GenericLab/o--Indosluch.EM--o/LM386_Indosluch_DIY/Early Versions/handDrawn_Indosluch.png

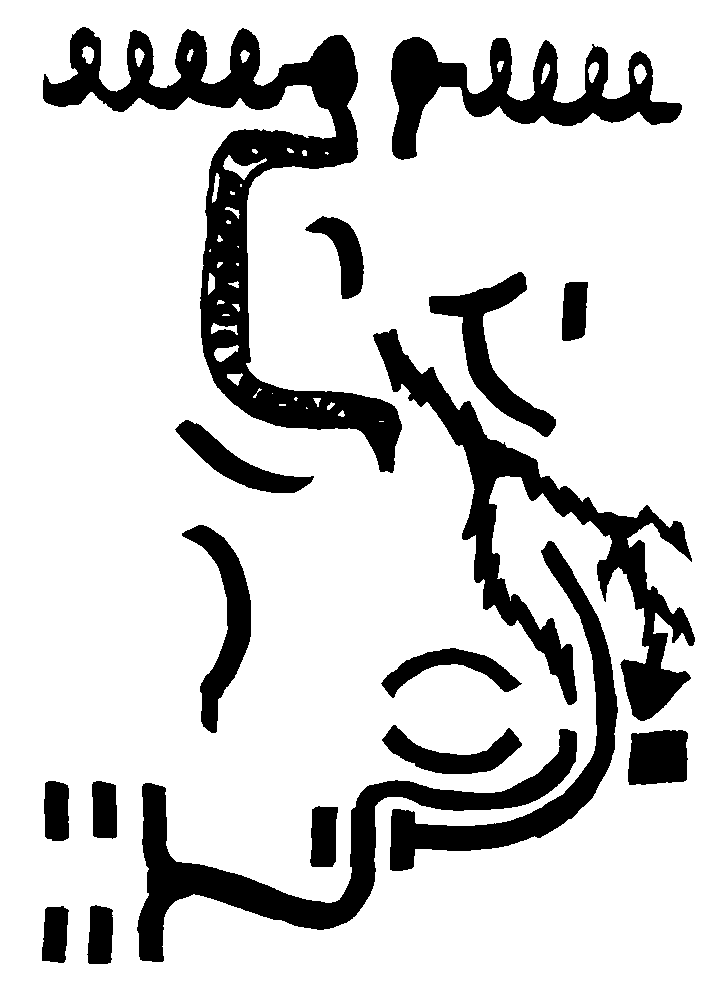
LM386_Indosluch_DIY/Early Versions/handDrawn_Indosluch.png
