GenericLab/o--Indosluch.EM--o/LM386_Indosluch_DIY/Early Versions/MASK_LM386_Indosluch_DIY.png

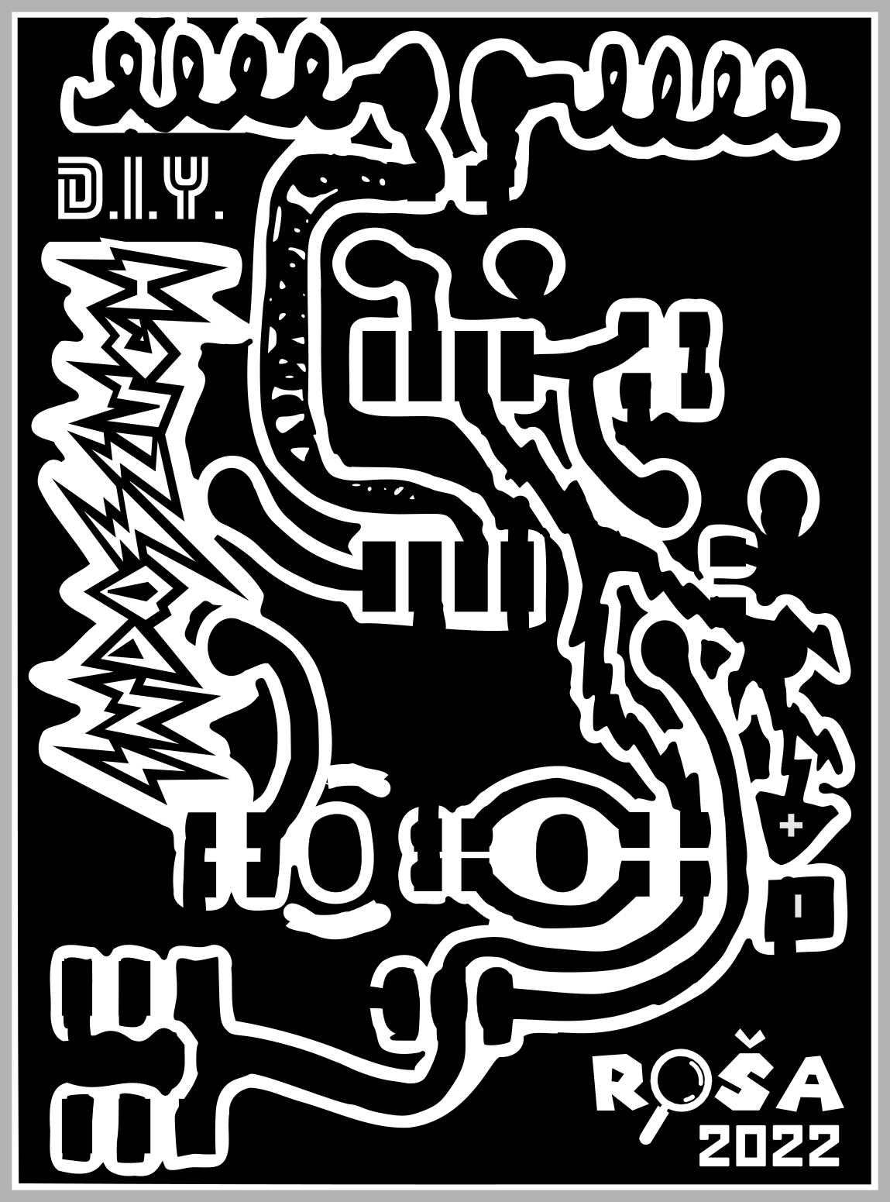
LM386_Indosluch_DIY/Early Versions/MASK_LM386_Indosluch_DIY.png
