GenericLab/o--Indosluch.EM--o/LM386_Indosluch_DIY/Engraving_Indosluch_DIY.png

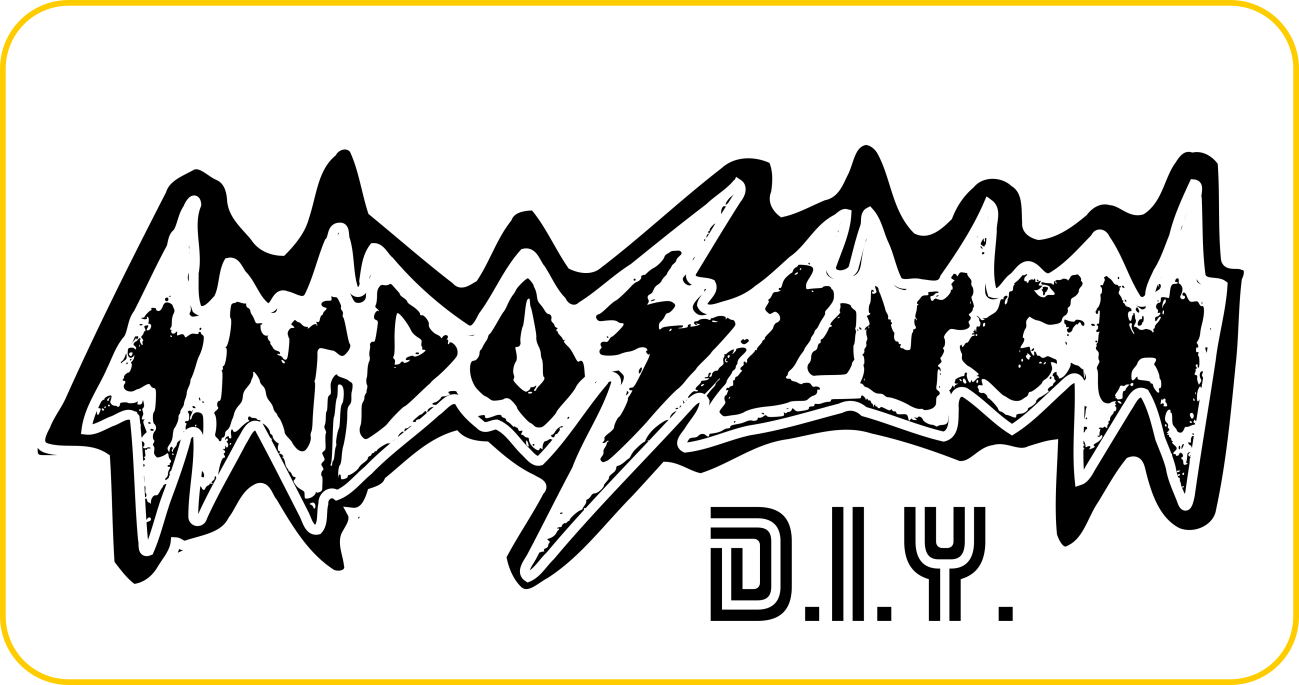
LM386_Indosluch_DIY/Engraving_Indosluch_DIY.png
