GenericLab/o--Indosluch.EM--o/sources/ErrorLeaks/reverseEng_error-zapper.jpg

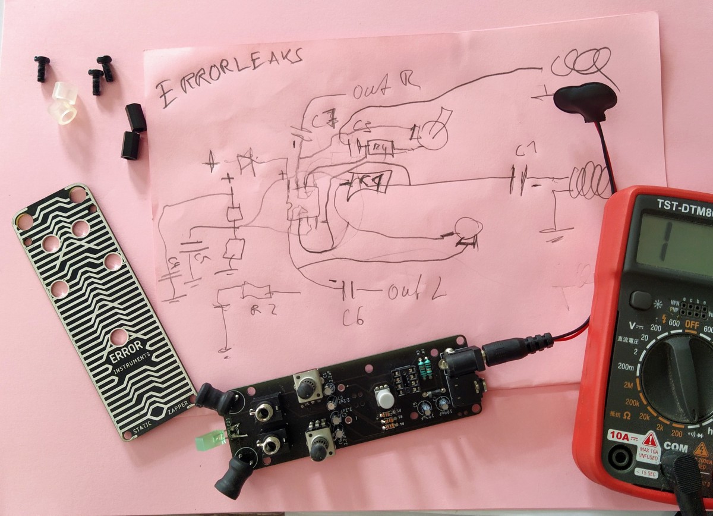
sources/ErrorLeaks/reverseEng_error-zapper.jpg
