GenericLab/o--Indosluch.EM--o/sources/ErrorLeaks/schema_error-zapper.jpg

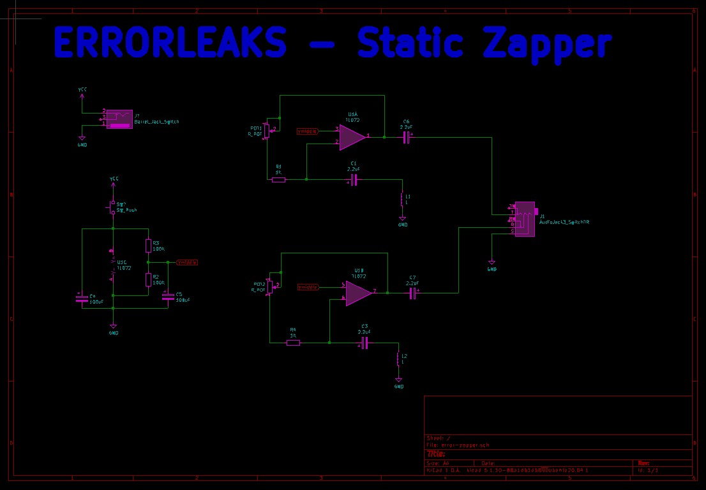
sources/ErrorLeaks/schema_error-zapper.jpg
