GenericLab/o--Indosluch.EM--o/sources/Franzis_Bat-Detector/Fledermaus11.jpg

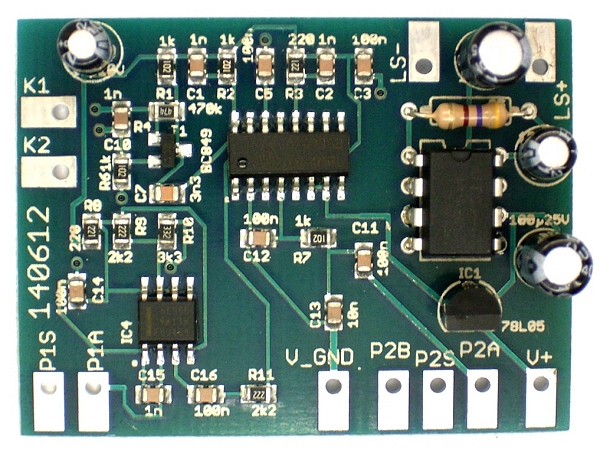
sources/Franzis_Bat-Detector/Fledermaus11.jpg
