GenericLab/o--Indosluch.EM--o/sources/MartinHowse_Detektor/1010_Detektor.jpg

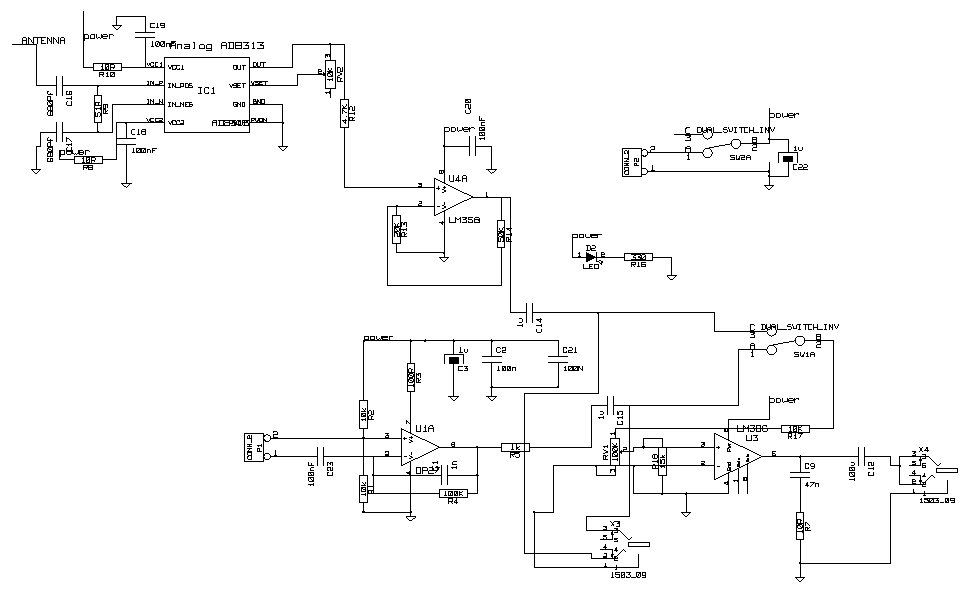
sources/MartinHowse_Detektor/1010_Detektor.jpg
