GenericLab/o--Indosluch.EM--o/sources/SOMA-EtherLeaks/Ether_ampStage.jpg

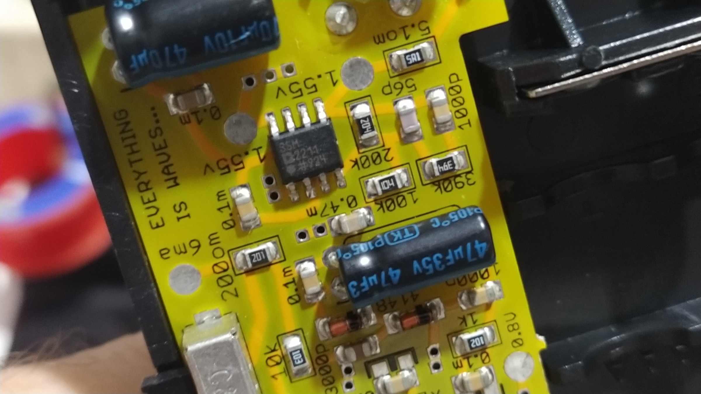
sources/SOMA-EtherLeaks/Ether_ampStage.jpg
