GenericLab/o--Indosluch.EM--o/sources/SOMA-EtherLeaks/Ether_AntennaArea.jpg

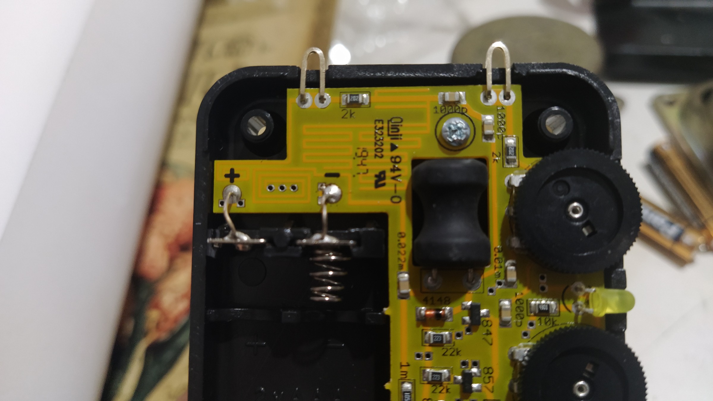
sources/SOMA-EtherLeaks/Ether_AntennaArea.jpg
