GenericLab/o--Indosluch.EM--o/sources/SOMA-EtherLeaks/Ether_Backside_full.jpg

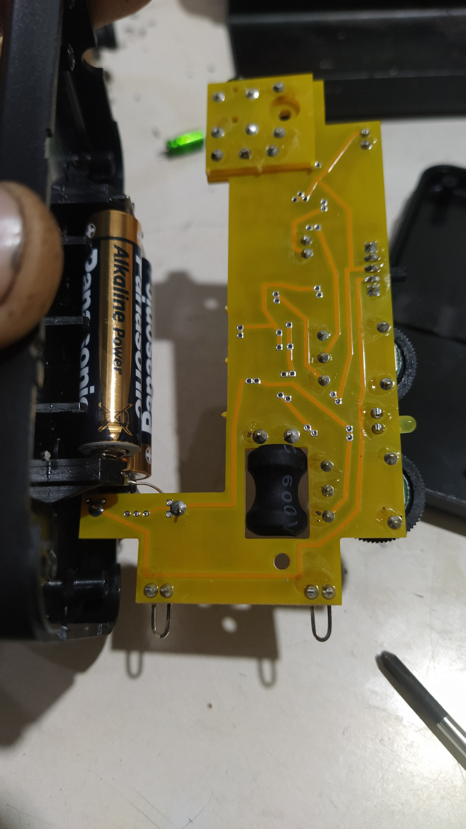
sources/SOMA-EtherLeaks/Ether_Backside_full.jpg
