GenericLab/o--Indosluch.EM--o/sources/SOMA-EtherLeaks/Ether_FrontSideFull.jpg

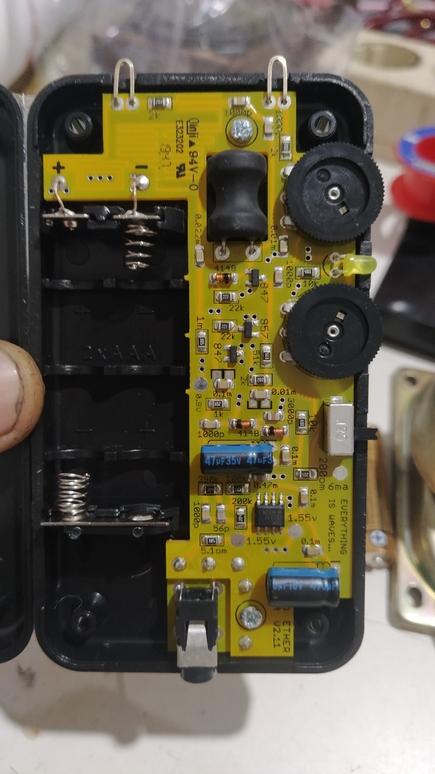
sources/SOMA-EtherLeaks/Ether_FrontSideFull.jpg
