GenericLab/o--Indosluch.EM--o/sources/Uwes_circuits/LM386 sniffer_ac.jpg

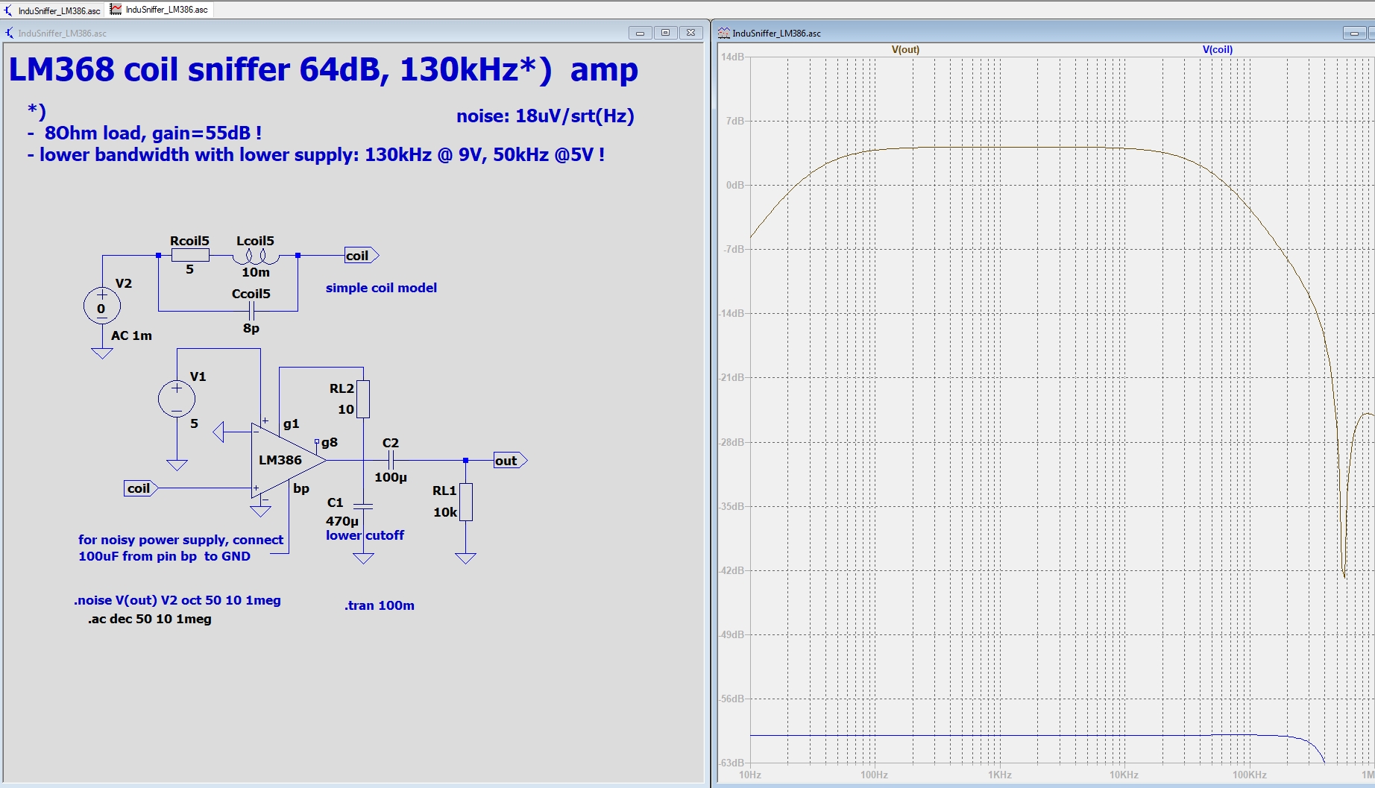
sources/Uwes_circuits/LM386 sniffer_ac.jpg
