GenericLab/o--Indosluch.EM--o/sources/Uwes_circuits/LM386 sniffer_noise.jpg

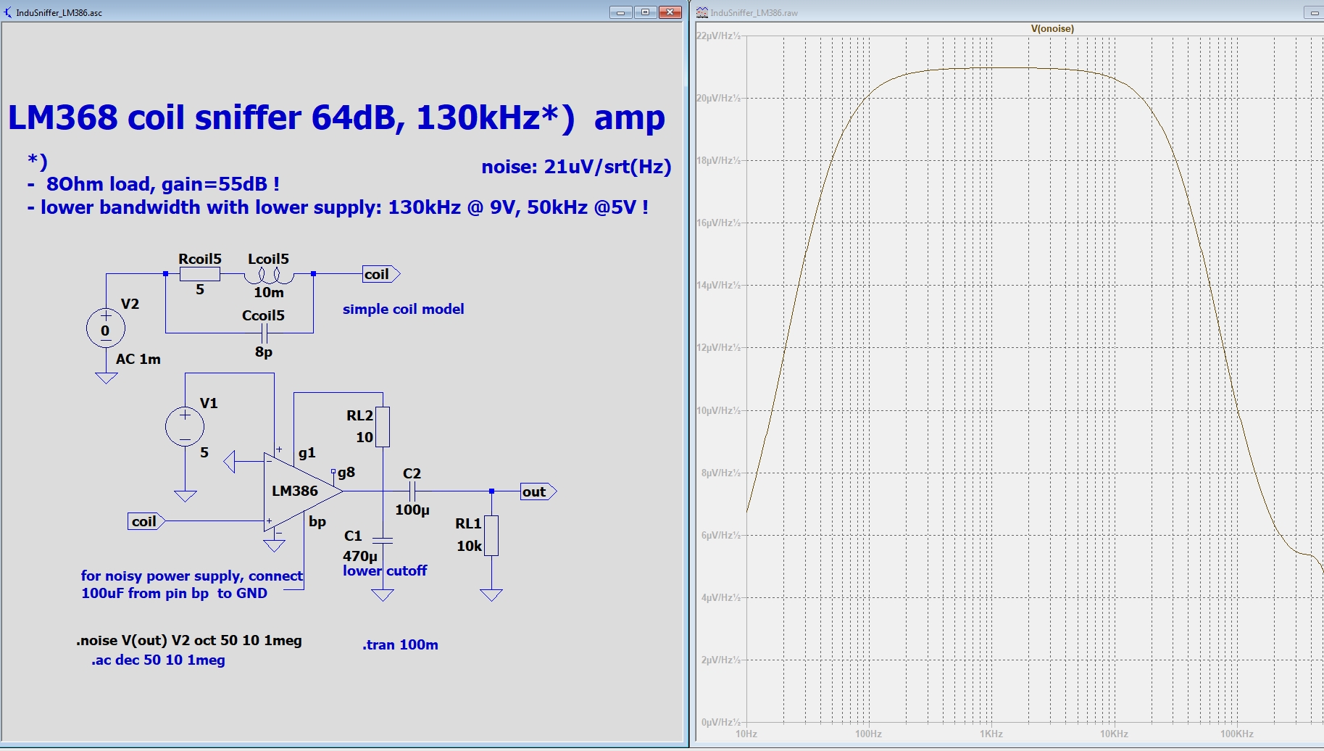
sources/Uwes_circuits/LM386 sniffer_noise.jpg
