GenericLab/o--Indosluch.EM--o/sources/Uwes_circuits/lm386.gif

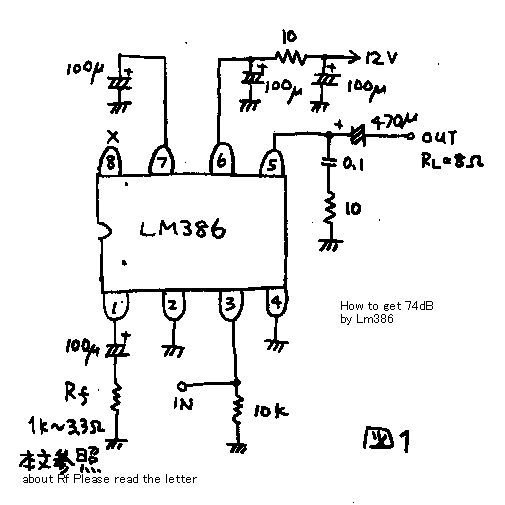
sources/Uwes_circuits/lm386.gif
