GenericLab/o--Indosluch.EM--o/sources/Uwes_circuits/NPN-PNP- sniffer_ac.jpg

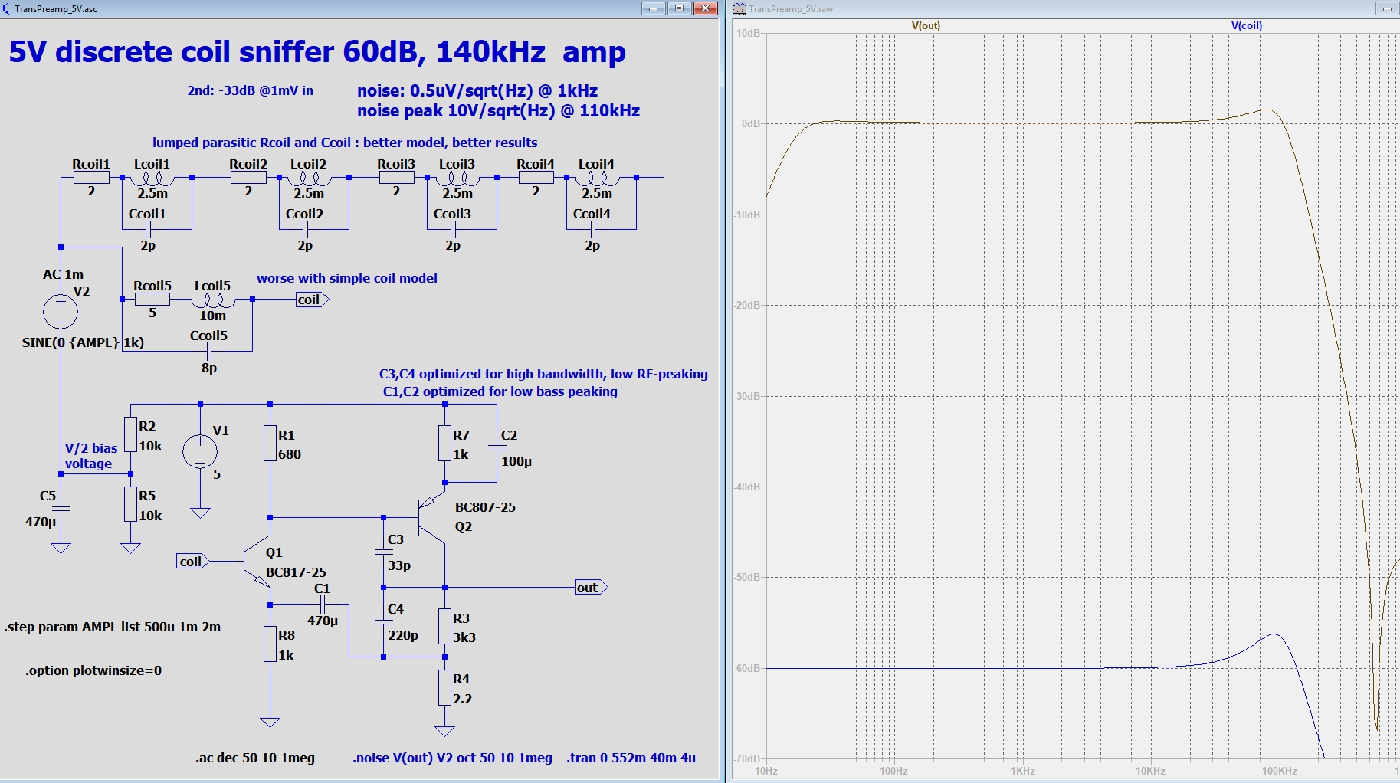
sources/Uwes_circuits/NPN-PNP- sniffer_ac.jpg
