GenericLab/o--Indosluch.EM--o/sources/Uwes_circuits/NPN-PNP- sniffer_noise.jpg

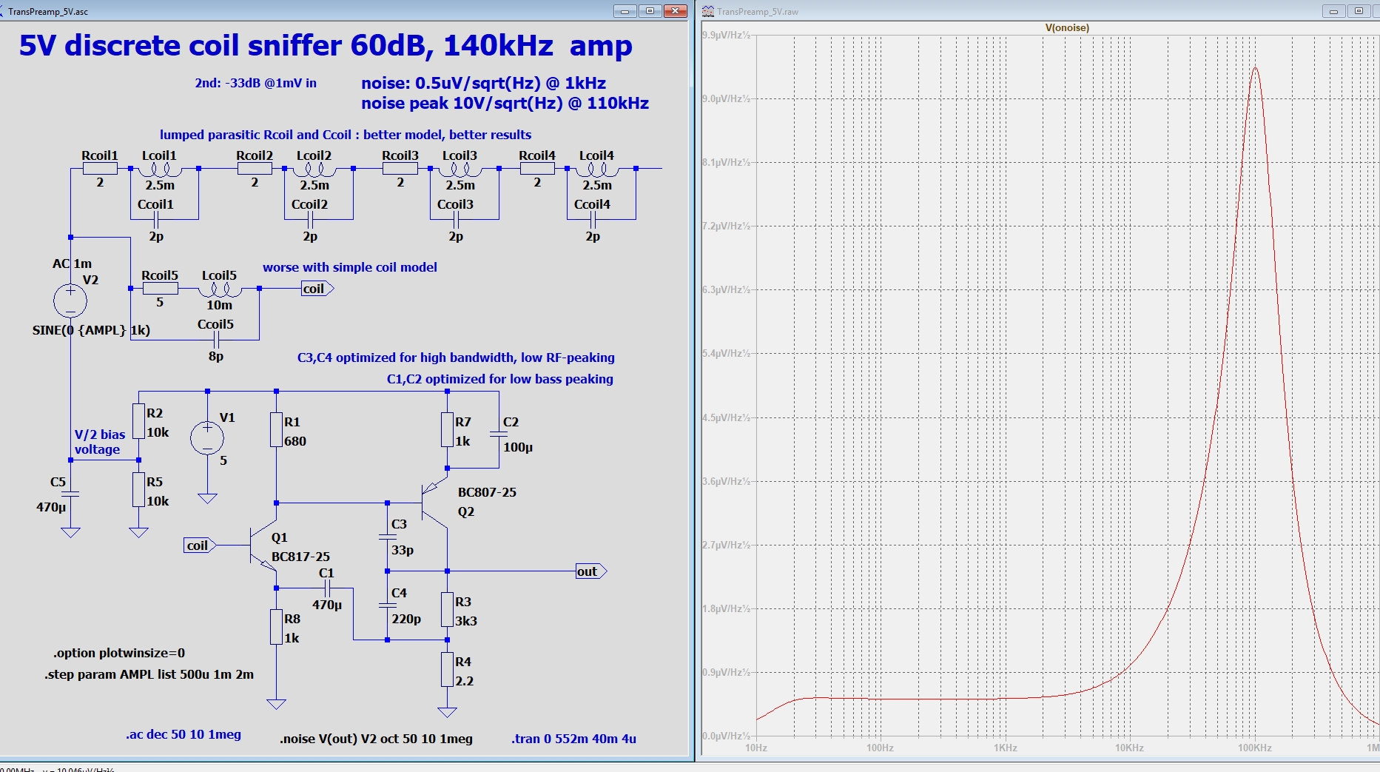
sources/Uwes_circuits/NPN-PNP- sniffer_noise.jpg
