GenericLab/o--Indosluch.EM--o/SSM2211_PowerAmp/MASK_SSM2211_amp.png

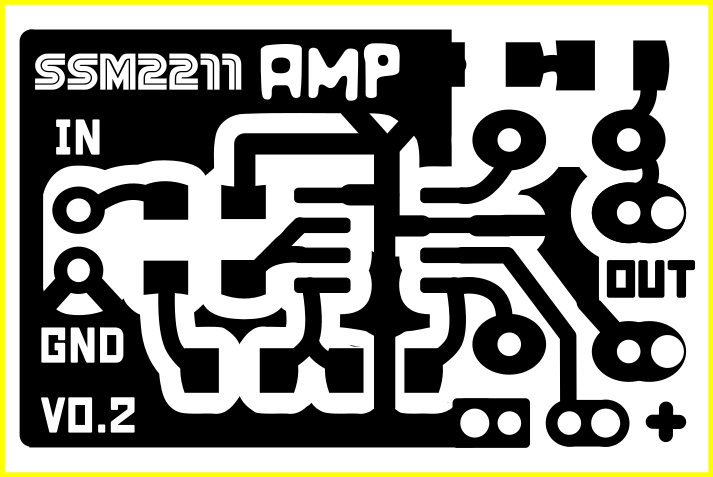
SSM2211_PowerAmp/MASK_SSM2211_amp.png
