GenericLab/o--Indosluch.EM--o/Indosluch_AM/Indosluch_AM_partsPlacement.jpg

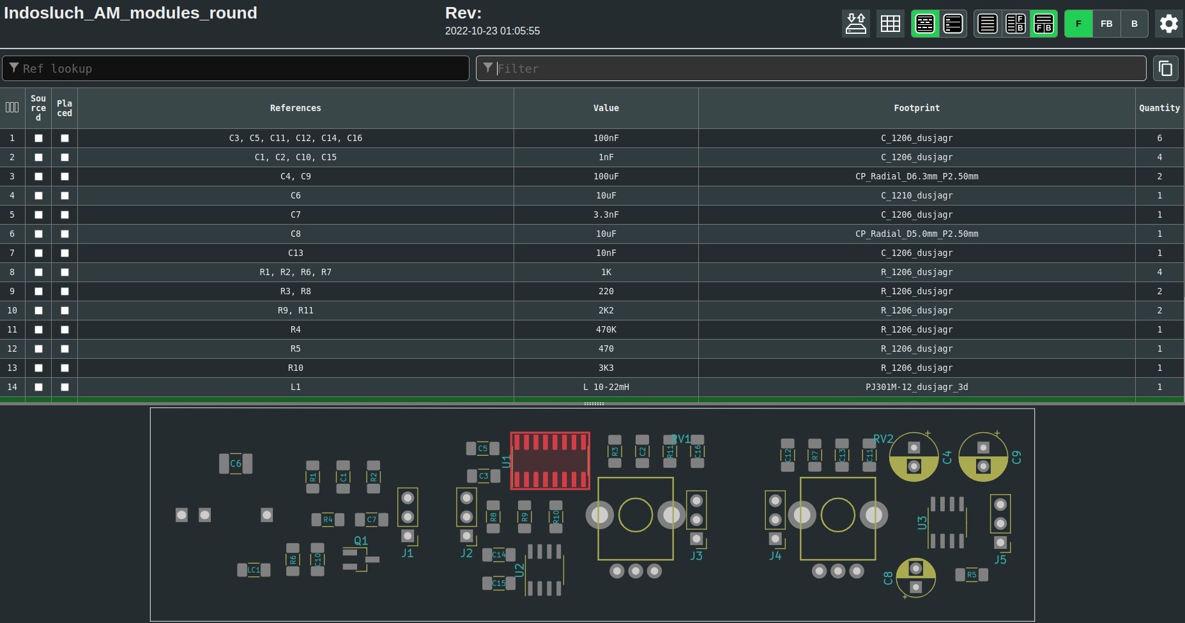
Indosluch_AM/Indosluch_AM_partsPlacement.jpg
