GenericLab/o--Indosluch.EM--o/Indosluch_AM/Indosluch_AM/MASK/SolderMask.png

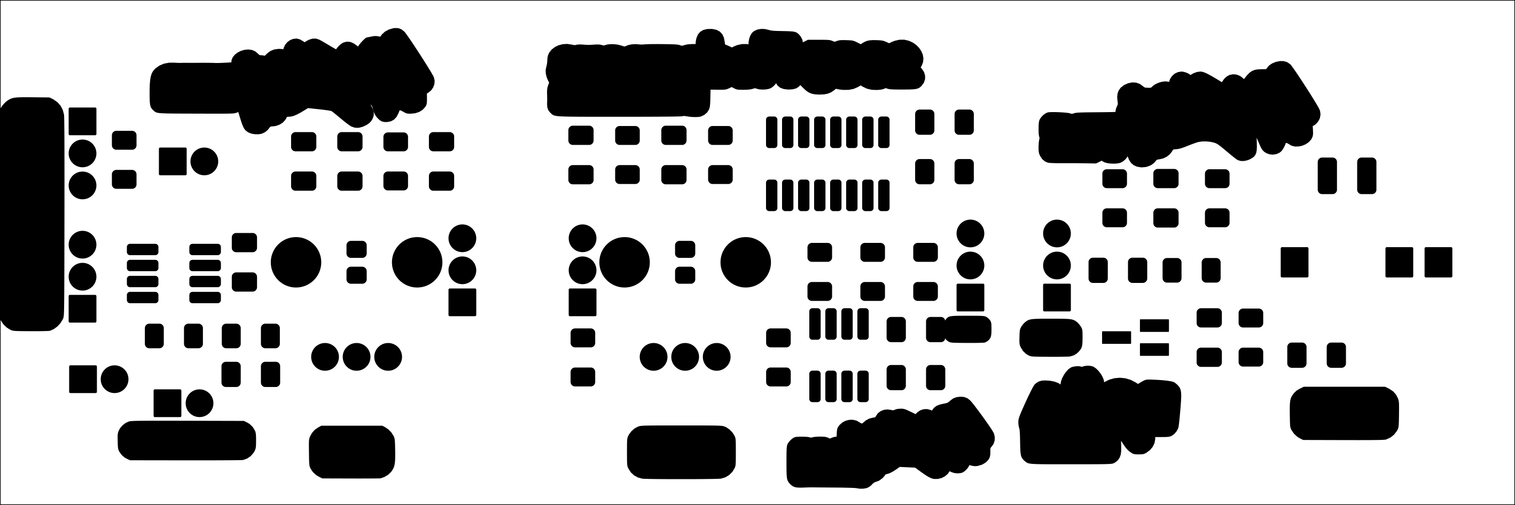
Indosluch_AM/Indosluch_AM/MASK/SolderMask.png
