GenericLab/o--Indosluch.EM--o/LM386_Indosluch_DIY/Early Versions/SolderMASK_LM386_Indosluch_DIY.png

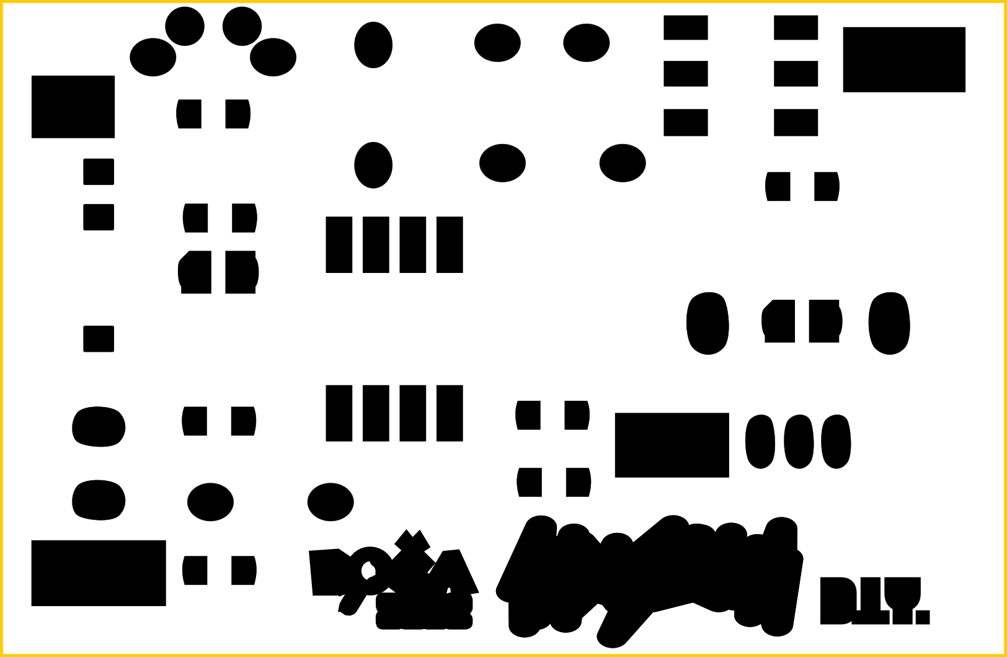
LM386_Indosluch_DIY/Early Versions/SolderMASK_LM386_Indosluch_DIY.png
